CrazyRobMiles/PICO-Camera-Cable-Release-Controller/python/boot.py

import storage
import usb_cdc

# Disable USB mass storage
storage.disable_usb_drive()

# Keep USB REPL enabled to allow deploying files via REPL tools
usb_cdc.enable(console=True, data=True)

# Remount the filesystem so CircuitPython code can write to it
storage.remount("/", readonly=False)
